peauters/peautkb/firmware/src/dispatcher/info.rs

use crate::multi::{Multi, Multi::*};

use super::*;

use embedded_graphics::{
    fonts::{Font6x8, Text},
    pixelcolor::BinaryColor,
    style::TextStyleBuilder,
};
use keyberon::layout::Event;

#[derive(Default)]
pub struct Info {
    usb_connected: bool,
    hand: Option<Hand>,
    last_matrix: Option<Event>,
    cmd_held: bool,
    ctrl_held: bool,
    current_layer: Layer,
    ticks_since_press: u32,
}

impl Info {
    fn tick(&mut self) -> Multi<Message> {
        self.ticks_since_press = self.ticks_since_press.saturating_add(1);

        if self.ticks_since_press > 3 * 60 * 24 {
            One(Message::Sleep)
        } else {
            None
        }
    }

    fn press(&mut self) -> Multi<Message> {
        if self.ticks_since_press > 3 * 60 * 24 {
            self.ticks_since_press = 0;
            One(Message::Wake)
        } else {
            self.ticks_since_press = 0;
            None
        }
    }
}

const fn bool_to_string(b: bool) -> &'static str {
    match b {
        true => "true",
        false => "false",
    }
}

impl super::State for Info {
    type Messages = Multi<Message>;
    fn write_to_display<DI, DSIZE>(&mut self, display: &mut GraphicsMode<DI, DSIZE>)
    where
        DSIZE: DisplaySize,
        DI: WriteOnlyDataCommand,
    {
        display.clear();

        let font_6x8 = TextStyleBuilder::new(Font6x8)
            .text_color(BinaryColor::On)
            .build();

        Text::new("hand:", Point::zero())
            .into_styled(font_6x8)
            .draw(display)
            .unwrap();

        let hand = match self.hand {
            Some(Hand::Left) => "left",
            Some(Hand::Right) => "right",
            Option::None => "",
        };

        Text::new(hand, Point::new(36, 0))
            .into_styled(font_6x8)
            .draw(display)
            .unwrap();

        Text::new("usb:", Point::new(0, 13))
            .into_styled(font_6x8)
            .draw(display)
            .unwrap();

        let usb = bool_to_string(self.usb_connected);

        Text::new(usb, Point::new(30, 13))
            .into_styled(font_6x8)
            .draw(display)
            .unwrap();

        Text::new("layer:", Point::new(0, 26))
            .into_styled(font_6x8)
            .draw(display)
            .unwrap();
        Text::new(self.current_layer.into(), Point::new(0, 39))
            .into_styled(font_6x8)
            .draw(display)
            .unwrap();

        if self.hand == Some(Hand::Left) {
            Text::new("cmd:", Point::new(0, 52))
                .into_styled(font_6x8)
                .draw(display)
                .unwrap();
            let cmd = bool_to_string(self.cmd_held);
            Text::new(cmd, Point::new(30, 52))
                .into_styled(font_6x8)
                .draw(display)
                .unwrap();
            Text::new("ctrl:", Point::new(0, 65))
                .into_styled(font_6x8)
                .draw(display)
                .unwrap();
            let ctrl = bool_to_string(self.ctrl_held);
            Text::new(ctrl, Point::new(36, 65))
                .into_styled(font_6x8)
                .draw(display)
                .unwrap();
        }

        display.flush().unwrap();
    }

    fn handle_event(&mut self, message: Message) -> Self::Messages {
        match message {
            Message::YouArePrimary => {
                defmt::info!("I am primary");
                self.hand = Some(Hand::Left);
                None
            }
            Message::YouAreSecondary => {
                defmt::info!("I am secondary");
                self.hand = Some(Hand::Right);
                None
            }
            Message::UsbConnected(is_connected) => {
                defmt::info!("Usb is connected");
                self.usb_connected = is_connected;
                None
            }
            Message::MatrixKeyPress(i, j) => {
                self.last_matrix = Some(Event::Press(i, j));
                self.press().add(if !self.usb_connected {
                    One(Message::SecondaryKeyPress(i, 13 - j))
                } else {
                    None
                })
            }
            Message::MatrixKeyRelease(i, j) => {
                self.last_matrix = Some(Event::Release(i, j));
                if !self.usb_connected {
                    One(Message::SecondaryKeyRelease(i, 13 - j))
                } else {
                    None
                }
            }
            Message::CurrentLayer(layer) => {
                self.current_layer = layer;
                One(Message::SecondaryCurrentLayer(layer))
            }
            Message::SecondaryCurrentLayer(layer) => {
                self.current_layer = layer;
                None
            }
            Message::CmdHeld => {
                self.cmd_held = true;
                None
            }
            Message::CmdReleased => {
                self.cmd_held = false;
                None
            }
            Message::CtrlHeld => {
                self.ctrl_held = true;
                None
            }
            Message::CtrlReleased => {
                self.ctrl_held = false;
                None
            }
            Message::Ping => One(Message::Pong),
            Message::UpdateDisplay => self.tick(),
            _ => None,
        }
    }
}

#[derive(Copy, Clone, PartialEq, Eq)]
pub enum Hand {
    Left,
    Right,
}
