peauters/peautkb/firmware/src/multi.rs

#[derive(Copy, Clone)]
pub enum Multi<T> {
    None,
    One(T),
    Two(T, T),
    Three(T, T, T),
    Four(T, T, T, T),
}

impl<T> Multi<T> {
    pub fn take(&mut self) -> Option<T> {
        match core::mem::take(self) {
            Multi::None => None,
            Multi::One(t) => {
                *self = Multi::None;
                Some(t)
            }
            Multi::Two(t, r) => {
                *self = Multi::One(r);
                Some(t)
            }
            Multi::Three(t, r, s) => {
                *self = Multi::Two(r, s);
                Some(t)
            }
            Multi::Four(t, r, s, x) => {
                *self = Multi::Three(r, s, x);
                Some(t)
            }
        }
    }

    pub fn push(&mut self, t: T) {
        match core::mem::take(self) {
            Multi::None => *self = Multi::One(t),
            Multi::One(r) => *self = Multi::Two(t, r),
            Multi::Two(r, s) => *self = Multi::Three(t, r, s),
            Multi::Three(r, s, x) => *self = Multi::Four(t, r, s, x),
            _ => *self = Multi::None,
        }
    }

    pub fn append(&mut self, x: T) {
        match core::mem::take(self) {
            Multi::None => *self = Multi::One(x),
            Multi::One(t) => *self = Multi::Two(t, x),
            Multi::Two(t, r) => *self = Multi::Three(t, r, x),
            Multi::Three(t, r, s) => *self = Multi::Four(t, r, s, x),
            _ => *self = Multi::None,
        }
    }

    pub fn add(self, other: Multi<T>) -> Multi<T> {
        match (self, other) {
            (a, Multi::None) => a,
            (Multi::None, other) => other,
            (Multi::One(t), Multi::One(r)) => Multi::Two(t, r),
            (Multi::One(t), Multi::Two(r, s)) => Multi::Three(t, r, s),
            (Multi::One(t), Multi::Three(r, s, x)) => Multi::Four(t, r, s, x),
            (Multi::Two(t, r), Multi::One(s)) => Multi::Three(t, r, s),
            (Multi::Two(t, r), Multi::Two(s, x)) => Multi::Four(t, r, s, x),
            (Multi::Three(t, r, s), Multi::One(x)) => Multi::Four(t, r, s, x),
            _ => Multi::None,
        }
    }
}

impl<T> Default for Multi<T> {
    fn default() -> Self {
        Multi::None
    }
}

impl<T> IntoIterator for Multi<T> {
    type Item = T;
    type IntoIter = MultiIter<T>;

    fn into_iter(self) -> Self::IntoIter {
        MultiIter(self)
    }
}

pub struct MultiIter<T>(Multi<T>);

impl<T> Iterator for MultiIter<T> {
    type Item = T;

    fn next(&mut self) -> Option<T> {
        self.0.take()
    }
}
